aathmaj/pixelplay/assets/renders/0001.png

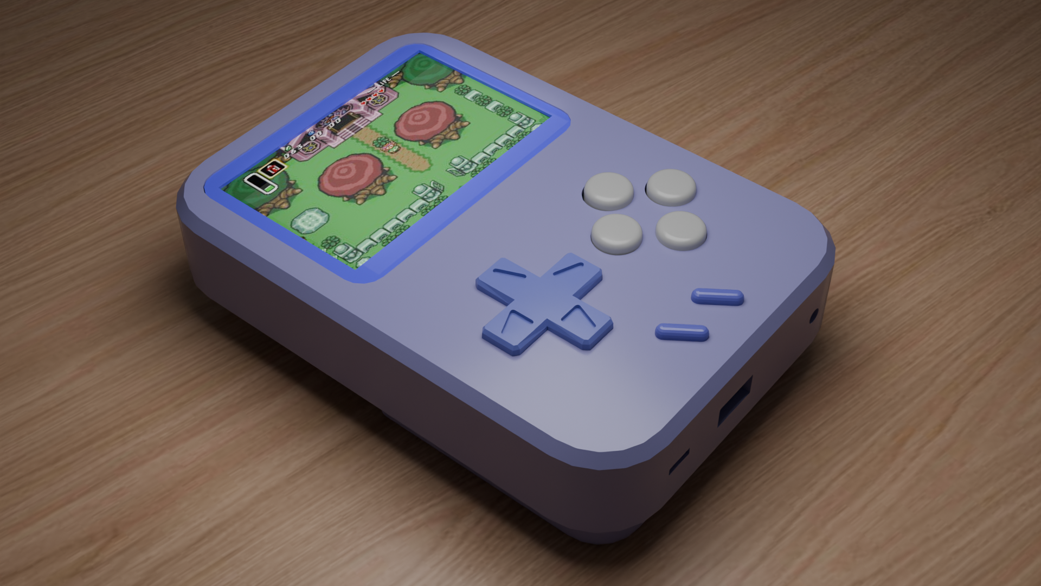
assets/renders/0001.png
