aathmaj/pixelplay/assets/renders/0003.png

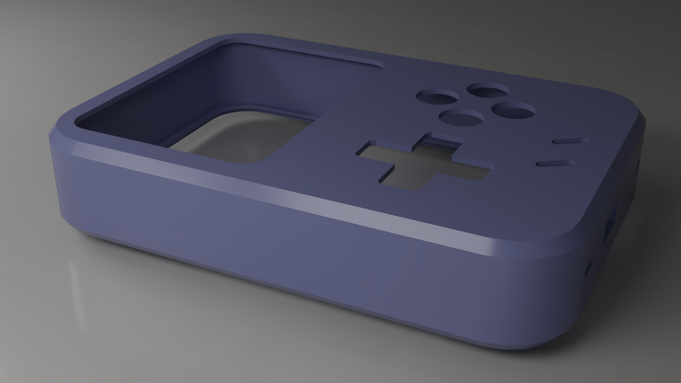
assets/renders/0003.png
