aathmaj/pixelplay/assets/renders/0004.png

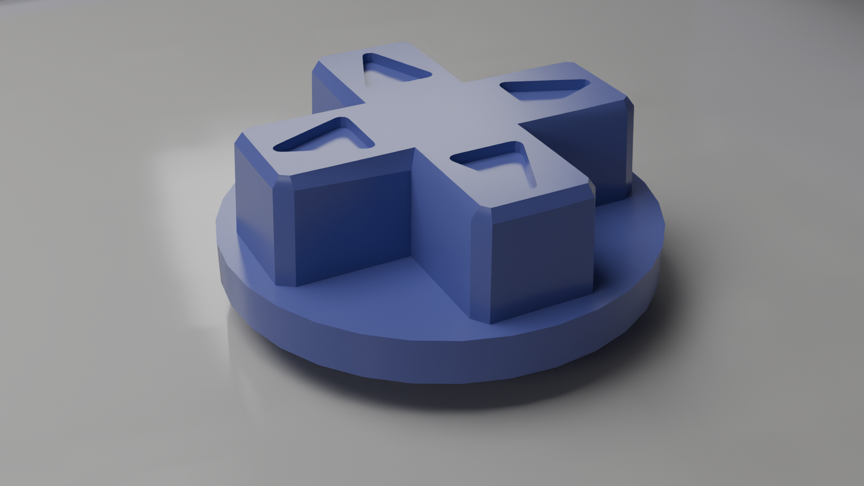
assets/renders/0004.png
