aathmaj/pixelplay/assets/renders/0005.png

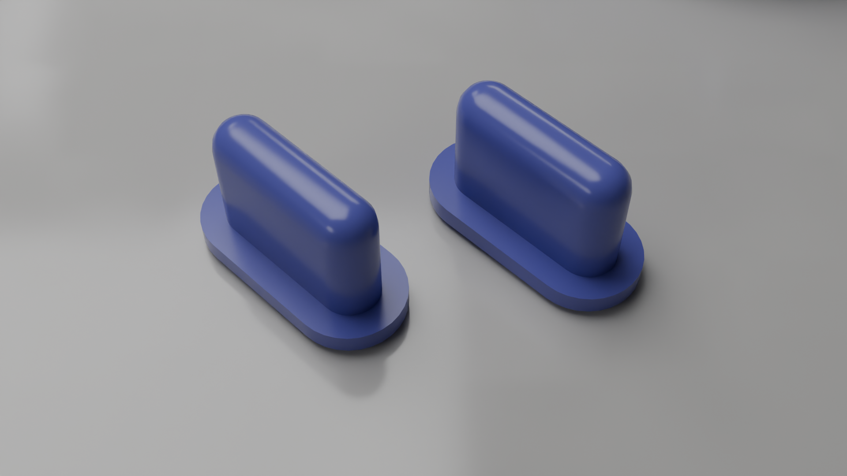
assets/renders/0005.png
