aathmaj/pixelplay/assets/renders/0007.png

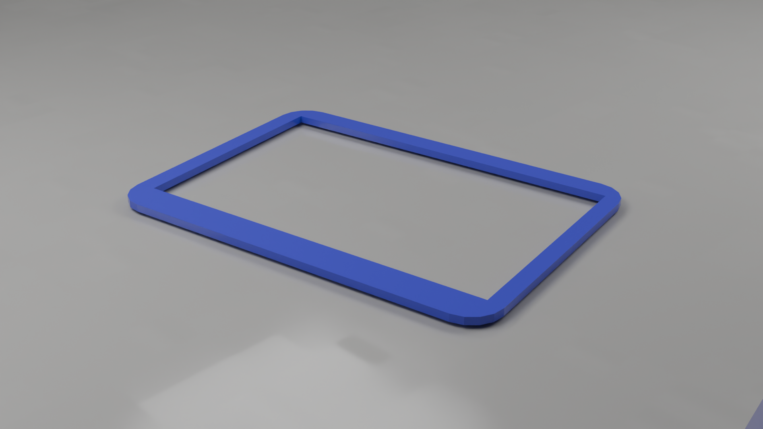
assets/renders/0007.png
